pizzalover125/sten0/PCB/sten0.kicad_sch

## KiCad design PCB/sten0.kicad_sch (2026-05-23)

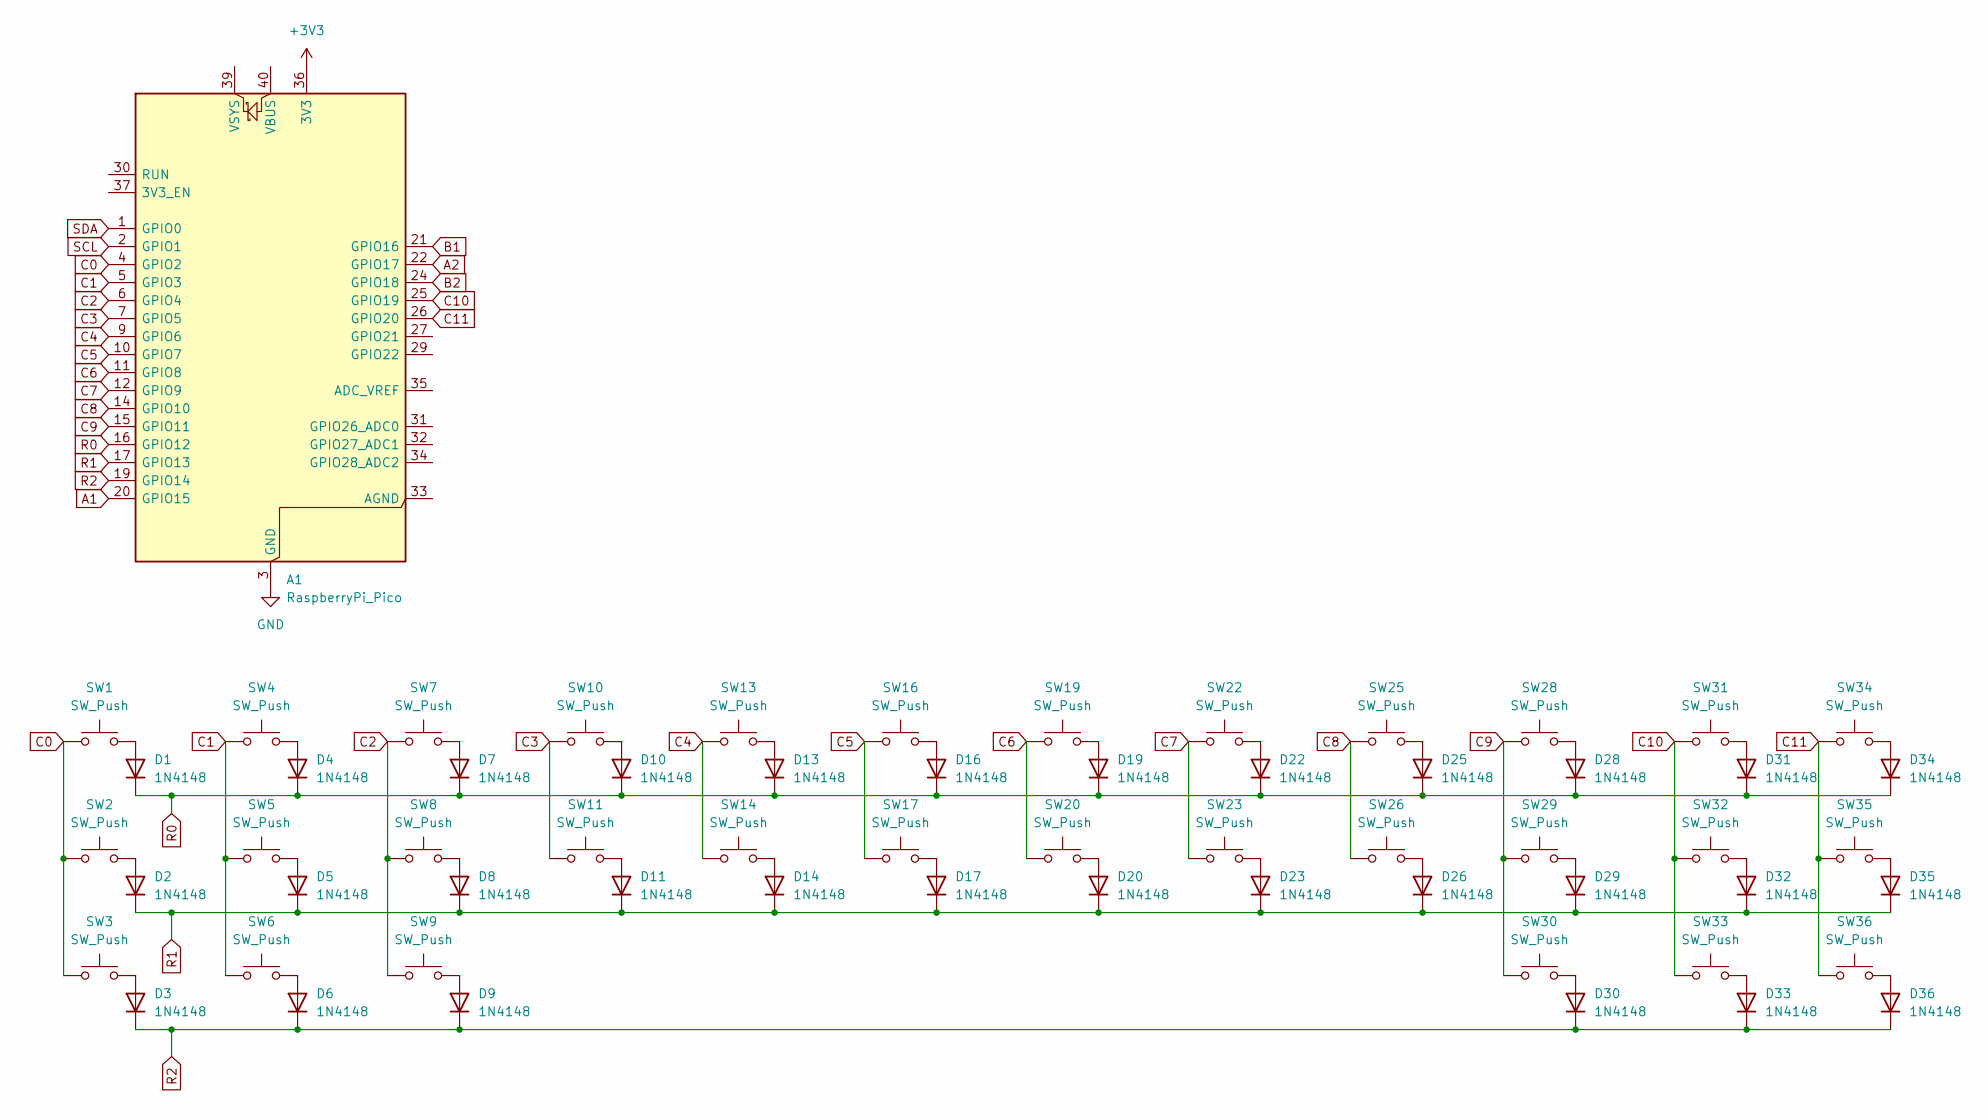
[picture p11: schematic sten0.kicad_sch]

Parts:
A1: RaspberryPi_Pico; RaspberryPi_Pico_Common_Unspecified
D1, D2, D3, D4, D5, D6, D7, D8, D9, D10, D11, D13, D14, D16, D17, D19, D20, D22, D23, D25, D26, D28, D29, D30, D31, D32, D33, D34, D35, D36: 1N4148; D_DO-35_SOD27_P7.62mm_Horizontal
SW1, SW2, SW3, SW4, SW5, SW6, SW7, SW8, SW9, SW10, SW11, SW13, SW14, SW16, SW17, SW19, SW20, SW22, SW23, SW25, SW26, SW28, SW29, SW30, SW31, SW32, SW33, SW34, SW35, SW36: SW_Push; SW_PG1350

Connections:
+3V3: A1.36 (3V3)
A1: A1.20 (GPIO15)
A2: A1.22 (GPIO17)
B1: A1.21 (GPIO16)
B2: A1.24 (GPIO18)
C0: A1.4 (GPIO2), SW1.1, SW2.1, SW3.1
C1: A1.5 (GPIO3), SW4.1, SW5.1, SW6.1
C2: A1.6 (GPIO4), SW7.1, SW8.1, SW9.1
C3: A1.7 (GPIO5), SW10.1, SW11.1
C4: A1.9 (GPIO6), SW13.1, SW14.1
C5: A1.10 (GPIO7), SW16.1, SW17.1
C6: A1.11 (GPIO8), SW19.1, SW20.1
C7: A1.12 (GPIO9), SW22.1, SW23.1
C8: A1.14 (GPIO10), SW25.1, SW26.1
C9: A1.15 (GPIO11), SW28.1, SW29.1, SW30.1
C10: A1.25 (GPIO19), SW31.1, SW32.1, SW33.1
C11: A1.26 (GPIO20), SW34.1, SW35.1, SW36.1
GND: A1.3 (GND), A1.8 (GND), A1.13 (GND), A1.18 (GND), A1.23 (GND), A1.28 (GND), A1.38 (GND)
unnamed: D1.2 (A), SW1.2
unnamed: D2.2 (A), SW2.2
unnamed: D3.2 (A), SW3.2
unnamed: D4.2 (A), SW4.2
unnamed: D5.2 (A), SW5.2
unnamed: D6.2 (A), SW6.2
unnamed: D7.2 (A), SW7.2
unnamed: D8.2 (A), SW8.2
unnamed: D9.2 (A), SW9.2
unnamed: D10.2 (A), SW10.2
unnamed: D11.2 (A), SW11.2
unnamed: D13.2 (A), SW13.2
unnamed: D14.2 (A), SW14.2
unnamed: D16.2 (A), SW16.2
unnamed: D17.2 (A), SW17.2
unnamed: D19.2 (A), SW19.2
unnamed: D20.2 (A), SW20.2
unnamed: D22.2 (A), SW22.2
unnamed: D23.2 (A), SW23.2
unnamed: D25.2 (A), SW25.2
unnamed: D26.2 (A), SW26.2
unnamed: D28.2 (A), SW28.2
unnamed: D29.2 (A), SW29.2
unnamed: D30.2 (A), SW30.2
unnamed: D31.2 (A), SW31.2
unnamed: D32.2 (A), SW32.2
unnamed: D33.2 (A), SW33.2
unnamed: D34.2 (A), SW34.2
unnamed: D35.2 (A), SW35.2
unnamed: D36.2 (A), SW36.2
R0: A1.16 (GPIO12), D1.1 (K), D4.1 (K), D7.1 (K), D10.1 (K), D13.1 (K), D16.1 (K), D19.1 (K), D22.1 (K), D25.1 (K), D28.1 (K), D31.1 (K), D34.1 (K)
R1: A1.17 (GPIO13), D2.1 (K), D5.1 (K), D8.1 (K), D11.1 (K), D14.1 (K), D17.1 (K), D20.1 (K), D23.1 (K), D26.1 (K), D29.1 (K), D32.1 (K), D35.1 (K)
R2: A1.19 (GPIO14), D3.1 (K), D6.1 (K), D9.1 (K), D30.1 (K), D33.1 (K), D36.1 (K)
SCL: A1.2 (GPIO1)
SDA: A1.1 (GPIO0)
